grotter/ArduinoAQI/ArduinoAQIData.cpp

#include "ArduinoAQIData.h"

ArduinoAQIData::ArduinoAQIData() {
  EEPROM.begin(512);
}

void ArduinoAQIData::begin() {  
  Credentials myCredentials = getSavedCredentials();
  
  _wifiManager.setSavedSsid(myCredentials.ssid);
  _wifiManager.setSavedPassword(myCredentials.password);
  
  _wifiManager.setDebugOutput(true);
  _wifiManager.setConfigPortalTimeout(300);

  _wifiManager.setSaveConfigCallback([]() -> void {
    Serial.println("WiFi config saved");
  });
  
  _wifiManager.autoConnect(ACCESS_POINT, ACCESS_POINT_PASSWORD);
  
  _onWifiConnect();
}

bool ArduinoAQIData::isConnected() {
  return WiFi.status() == WL_CONNECTED;
}

void ArduinoAQIData::setAPCallback( void (*func)(WiFiManager* myWiFiManager) ) {
  _wifiManager.setAPCallback(func);
}

bool ArduinoAQIData::write(float number1, float number2, float number3, float number4) {
  if (!isConnected()) {
    Serial.println("No wifi connection, try reconnecting.");
    _connectionAttempts = 0;
    _reconnectWifi();
    return false;
  }
  
  if (!_isRegistered) {
    Serial.println("Not registered, cancel data send and load config…");
    _loadThingspeakConfig();
    return false;
  }

  Serial.println("Sending data…");  
  ThingSpeak.setField(1, number1);
  ThingSpeak.setField(2, number2);
  ThingSpeak.setField(3, number3);
  ThingSpeak.setField(4, number4);

  int x = ThingSpeak.writeFields(_thingspeakChannelId, _thingspeakWriteKey.c_str());

  if (x != OK_SUCCESS) {
    Serial.println("Error code: " + String(x)); 
  }
  
  if (x == ERR_CONNECT_FAILED) {
    Serial.println("ThingSpeak connection error!");
    _connectionAttempts = 0;
    _reconnectWifi();
    return false;
  }
  
  if (x == ERR_BADAPIKEY || x == ERR_BADURL) {
    Serial.println("Wrong API key or bad endpoint. Reload config…");
    _loadThingspeakConfig();
    return false;
  }

  if (x == ERR_NOT_INSERTED) {
    Serial.println("ThingSpeak write failed! Probably reached rate limit."); 
  }
  
  return x == OK_SUCCESS;
}

void ArduinoAQIData::restart() {
  // @see
  // https://github.com/esp8266/Arduino/issues/1722
  Serial.println("ESP.restart does not work the first time after serial flashing.");
  ESP.restart();
}

void ArduinoAQIData::disconnectAndRestart(bool clearCredentials) {
  if (isConnected()) {
    WiFi.disconnect(clearCredentials);
    
    // wait for disconnect    
    int disconnectAttempts = 0;

    while(1) {
      disconnectAttempts++;

      if (WiFi.status() == WL_DISCONNECTED) {
        break;
      }
      
      if (disconnectAttempts >= MAX_DISCONNECT_ATTEMPTS) {
        break;
      }

      delay(1000);
    }
  }

  restart();
}

void ArduinoAQIData::resetWifi() {
  // clear credentials and restart
  _clearEEPROMCredentials();
  disconnectAndRestart(true);
}

String ArduinoAQIData::getMacAddress() {
  String myMac;
  
  byte mac[6];
  WiFi.macAddress(mac);

  myMac = String(mac[0], HEX) + ":";
  myMac += String(mac[1], HEX) + ":";
  myMac += String(mac[2], HEX) + ":";
  myMac += String(mac[3], HEX) + ":";
  myMac += String(mac[4], HEX) + ":";
  myMac += String(mac[5], HEX);
   
  return myMac; 
}

Credentials ArduinoAQIData::getSavedCredentials() {
  char ssid[WIFI_VARIABLE_LENGTH];
  char password[WIFI_VARIABLE_LENGTH];
  EEPROM.get(0, ssid);
  EEPROM.get(WIFI_VARIABLE_LENGTH, password);

  String mySsid = String(ssid);
  String myPassword = String(password);
  
  if (_isNull(0)) mySsid = "";
  if (_isNull(WIFI_VARIABLE_LENGTH)) myPassword = "";

  return {
    ssid: mySsid,
    password: myPassword
  };
}

void ArduinoAQIData::_clearEEPROMCredentials() {
  for (int i = 0; i < WIFI_VARIABLE_LENGTH * 2; i++) {
    EEPROM.write(i, 255);
  }

  EEPROM.commit();
}

void ArduinoAQIData::_reconnectWifi() {
  _connectionAttempts++;

  if (isConnected()) {
    Serial.println("Already connected, something is wonky. Try restarting…");
    restart();
    return;
  }
  
  // only try a few times, otherwise reset button is blocked
  if (_connectionAttempts > MAX_CONNECTION_ATTEMPTS) {
    Serial.println("Max connection attempts reached. Try restarting…");
    restart();
    return;
  }
  
  // retrieve saved credentials
  Credentials myCredentials = getSavedCredentials();

  if (myCredentials.ssid == "") {
    Serial.println("No EEPROM-stored credentials. Back to config…");
    resetWifi();
    return;
  }

  // attempt connection
  Serial.println("Attempting to reconnect to " + myCredentials.ssid + "… (" + _connectionAttempts + ")"); 
  WiFi.disconnect();
  _wifiManager.connectWifi(myCredentials.ssid, myCredentials.password);
  
  // success
  _onWifiConnect();
}

void ArduinoAQIData::_saveWifiCredentials() {
  // only save validated credentials
  if (!isConnected()) return;
  
  char mySsid[WIFI_VARIABLE_LENGTH];
  char myPassword[WIFI_VARIABLE_LENGTH];

  WiFi.SSID().toCharArray(mySsid, WIFI_VARIABLE_LENGTH);
  WiFi.psk().toCharArray(myPassword, WIFI_VARIABLE_LENGTH);
  
  EEPROM.put(0, mySsid);
  EEPROM.put(WIFI_VARIABLE_LENGTH, myPassword);
  EEPROM.commit();
  
  _wifiManager.setSavedSsid(WiFi.SSID());
  _wifiManager.setSavedPassword(WiFi.psk());
}

void ArduinoAQIData::_onWifiConnect () {
  Serial.println("_onWifiConnect");
  
  // no connection, retry
  if (!isConnected()) {
    _reconnectWifi();
    return;
  }

  // successfully joined as client
  _connectionAttempts = 0;
  
  Serial.println("MAC Address: " + getMacAddress());
  Serial.println("Connected to network: " + WiFi.SSID());

  // save credentials to EEPROM
  _saveWifiCredentials();

  // load ThingSpeak config
  _loadThingspeakConfig();
}

void ArduinoAQIData::_loadThingspeakConfig() {
  _isRegistered = false;
  ThingSpeak.begin(_client);

  if (!_fetchThingspeakConfig()) {
    _setDefaultThingspeakConfig();
  }
}

bool ArduinoAQIData::_fetchThingspeakConfig() {
  if (THINGSPEAK_REGISTRY_CHANNEL_NUMBER == 0) {
    Serial.println("No ThingSpeak registration channel configured");
    return false;
  }
  String json = ThingSpeak.readRaw(THINGSPEAK_REGISTRY_CHANNEL_NUMBER, String("/feeds/?results=8000"), THINGSPEAK_REGISTRY_API_KEY);
  int statusCode = ThingSpeak.getLastReadStatus();
  
  if (statusCode == OK_SUCCESS) {
    if (_setThingspeakConfig(json)) {
      _isRegistered = true;
      Serial.println("ThingSpeak registration complete.");
      return true;
    } else {
      Serial.println("ThingSpeak registration failed!");
    }
  } else {
    Serial.println("Failed to load ThingSpeak config from channel " + String(THINGSPEAK_REGISTRY_CHANNEL_NUMBER) +
                   "! Error code: " + String(statusCode));
  }
  return false;
}

void ArduinoAQIData::_setDefaultThingspeakConfig() {
  Serial.println("Using default ThingSpeak channel " + String(THINGSPEAK_DEFAULT_DATA_CHANNEL_NUMBER));
  _thingspeakChannelId = THINGSPEAK_DEFAULT_DATA_CHANNEL_NUMBER;
  _thingspeakWriteKey = THINGSPEAK_DEFAULT_DATA_WRITE_API_KEY;
  _isRegistered = true;
}

bool ArduinoAQIData::_setThingspeakConfig(String json) {
    int from = json.indexOf("[");
    if (from == -1) return false;

    int to = json.indexOf("]");
    if (to == -1) return false;
    
    // try parsing the JSON
    JSONVar feeds = JSON.parse(json.substring(from, to + 1));    
    if (JSON.typeof(feeds) != "array") return false;

    numRegisteredDevices = feeds.length();
    Serial.println("Number of registered devices: " + String(numRegisteredDevices));
    
    // iterate our ThingSpeak registration channel and match MAC addresses
    for (int i = 0; i < feeds.length(); i++) {
      JSONVar feed = feeds[i];

      if (feed.hasOwnProperty("field1") && feed.hasOwnProperty("field2")  && feed.hasOwnProperty("field3")) {
        const char* macAddress = feed["field1"];

        if (String(macAddress) == getMacAddress()) {
          // match found, set configuration
          const char* channelId = feed["field2"];
          _thingspeakChannelId = atoi(channelId);

          const char* writeKey = feed["field3"];
          _thingspeakWriteKey = String(writeKey);
          break;
        }
      }
    }

    return _thingspeakChannelId > 0;
}

bool ArduinoAQIData::_isNull(int loc) {
    // hack to check if first byte is 255 (assumed to be null)
    int firstChar = EEPROM.read(loc);
    return firstChar == 255;
}
